akerlund/rgb_driver_3ch/code/inc/gamma.h

#define GAMMA_LUT 0x0,0x0,0x0,0x0,0x0,0x0,0x0,0x0,0x0,0x0,0x0,0x0,0x0,0x0,0x0,0x0,0x0,0x0,0x0,0x0,0x0,0x0,0x0,0x0,0x0,0x0,0x0,0x0,0x0,0x0,0x0,0x0,0x0,0x0,0x0,0x0,0x0,0x0,0x0,0x0,0x0,0x0,0x0,0x0,0x0,0x0,0x0,0x0,0x0,0x0,0x0,0x0,0x0,0x0,0x0,0x0,0x0,0x0,0x0,0x0,0x0,0x0,0x0,0x0,0x0,0x0,0x0,0x0,0x0,0x0,0x0,0x0,0x0,0x0,0x0,0x0,0x0,0x0,0x0,0x0,0x0,0x0,0x0,0x0,0x0,0x0,0x0,0x0,0x0,0x0,0x0,0x0,0x0,0x0,0x0,0x0,0x0,0x0,0x0,0x0,0x0,0x0,0x0,0x0,0x0,0x0,0x0,0x0,0x0,0x0,0x0,0x0,0x0,0x0,0x0,0x0,0x0,0x0,0x0,0x0,0x0,0x0,0x0,0x0,0x0,0x0,0x0,0x0,0x0,0x0,0x0,0x0,0x0,0x0,0x0,0x0,0x0,0x0,0x0,0x0,0x0,0x0,0x0,0x0,0x0,0x0,0x0,0x0,0x0,0x0,0x0,0x0,0x0,0x0,0x0,0x0,0x0,0x0,0x0,0x0,0x0,0x0,0x0,0x0,0x0,0x0,0x0,0x0,0x0,0x0,0x0,0x0,0x0,0x0,0x0,0x0,0x0,0x0,0x0,0x0,0x0,0x0,0x0,0x0,0x0,0x0,0x0,0x0,0x0,0x0,0x0,0x0,0x0,0x1,0x1,0x1,0x1,0x1,0x1,0x1,0x1,0x1,0x1,0x1,0x1,0x1,0x1,0x1,0x1,0x1,0x1,0x1,0x1,0x1,0x1,0x1,0x1,0x1,0x1,0x1,0x1,0x1,0x1,0x1,0x1,0x1,0x1,0x1,0x1,0x1,0x1,0x1,0x1,0x1,0x1,0x1,0x1,0x1,0x1,0x1,0x1,0x1,0x1,0x1,0x1,0x1,0x1,0x1,0x2,0x2,0x2,0x2,0x2,0x2,0x2,0x2,0x2,0x2,0x2,0x2,0x2,0x2,0x2,0x2,0x2,0x2,0x2,0x2,0x2,0x2,0x2,0x2,0x2,0x2,0x2,0x2,0x2,0x2,0x2,0x2,0x2,0x2,0x2,0x2,0x2,0x2,0x2,0x2,0x3,0x3,0x3,0x3,0x3,0x3,0x3,0x3,0x3,0x3,0x3,0x3,0x3,0x3,0x3,0x3,0x3,0x3,0x3,0x3,0x3,0x3,0x3,0x3,0x3,0x3,0x3,0x3,0x3,0x3,0x3,0x3,0x4,0x4,0x4,0x4,0x4,0x4,0x4,0x4,0x4,0x4,0x4,0x4,0x4,0x4,0x4,0x4,0x4,0x4,0x4,0x4,0x4,0x4,0x4,0x4,0x4,0x4,0x4,0x4,0x5,0x5,0x5,0x5,0x5,0x5,0x5,0x5,0x5,0x5,0x5,0x5,0x5,0x5,0x5,0x5,0x5,0x5,0x5,0x5,0x5,0x5,0x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
